NowLoadY/Robophage/resource/code/Controller/yolo/data/images/bus.jpg

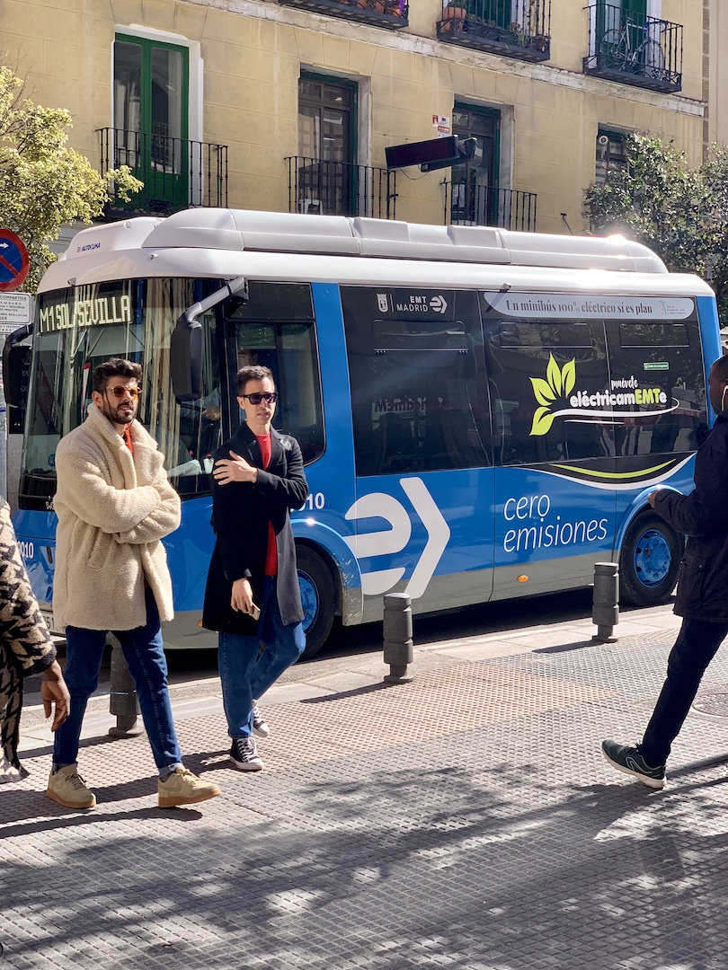
resource/code/Controller/yolo/data/images/bus.jpg
