NowLoadY/Robophage/resource/code/Controller/yolo/data/images/zidane.jpg

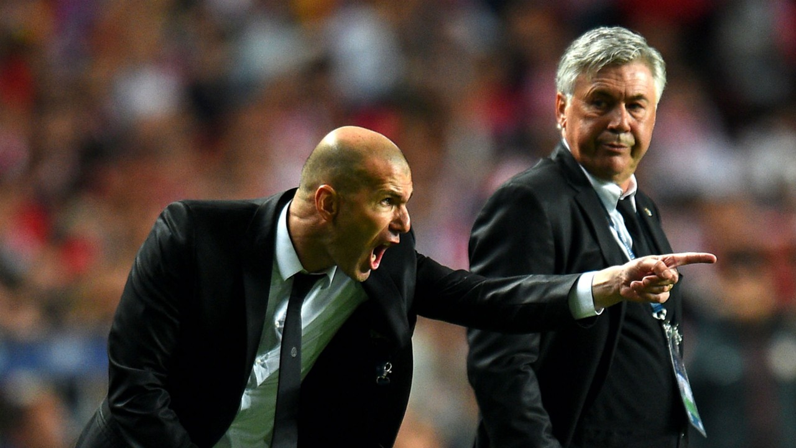
resource/code/Controller/yolo/data/images/zidane.jpg
