NowLoadY/Robophage/resource/StlFiles/foot/files/battery_lock.jpg

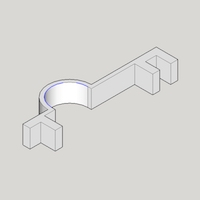
resource/StlFiles/foot/files/battery_lock.jpg
