NowLoadY/Robophage/resource/StlFiles/foot/files/body_back_wall.jpg

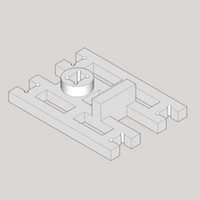
resource/StlFiles/foot/files/body_back_wall.jpg
