NowLoadY/Robophage/resource/StlFiles/foot/files/body_bottom.jpg

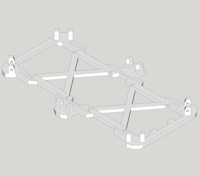
resource/StlFiles/foot/files/body_bottom.jpg
