NowLoadY/Robophage/resource/StlFiles/foot/files/body_center.jpg

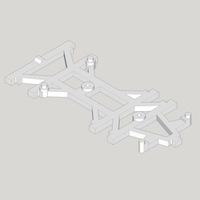
resource/StlFiles/foot/files/body_center.jpg
