NowLoadY/Robophage/resource/StlFiles/foot/files/body_side_wall.jpg

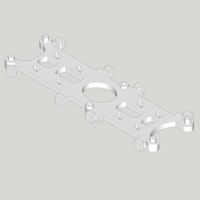
resource/StlFiles/foot/files/body_side_wall.jpg
