NowLoadY/Robophage/resource/StlFiles/foot/files/body_top.jpg

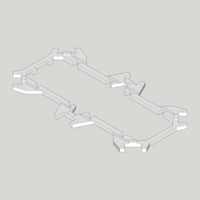
resource/StlFiles/foot/files/body_top.jpg
