NowLoadY/Robophage/resource/StlFiles/foot/files/foot_bottom.jpg

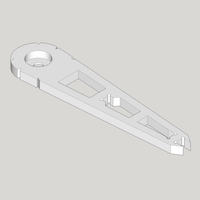
resource/StlFiles/foot/files/foot_bottom.jpg
