NowLoadY/Robophage/resource/StlFiles/foot/files/foot_ground.jpg

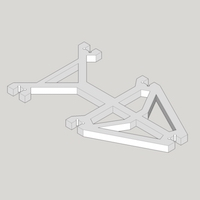
resource/StlFiles/foot/files/foot_ground.jpg
