NowLoadY/Robophage/resource/StlFiles/foot/files/foot_tip.jpg

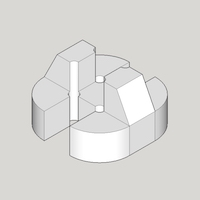
resource/StlFiles/foot/files/foot_tip.jpg
