NowLoadY/Robophage/resource/StlFiles/foot/files/foot_top.jpg

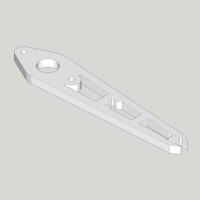
resource/StlFiles/foot/files/foot_top.jpg
