NowLoadY/Robophage/resource/StlFiles/foot/files/joint_bottom.jpg

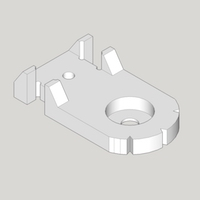
resource/StlFiles/foot/files/joint_bottom.jpg
