NowLoadY/Robophage/resource/StlFiles/foot/files/joint_cross.jpg

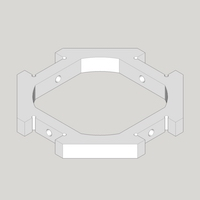
resource/StlFiles/foot/files/joint_cross.jpg
