NowLoadY/Robophage/resource/StlFiles/foot/files/joint_top.jpg

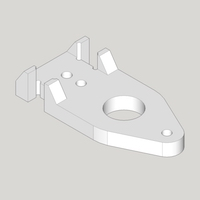
resource/StlFiles/foot/files/joint_top.jpg
