NowLoadY/Robophage/resource/StlFiles/foot/files/leg_bottom.jpg

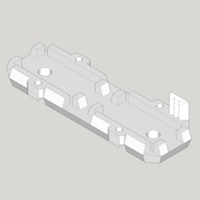
resource/StlFiles/foot/files/leg_bottom.jpg
