NowLoadY/Robophage/resource/StlFiles/foot/files/leg_top.jpg

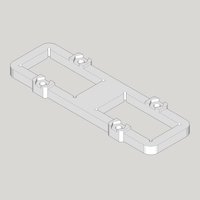
resource/StlFiles/foot/files/leg_top.jpg
