NowLoadY/Robophage/resource/StlFiles/foot/files/M2_6mm.JPG

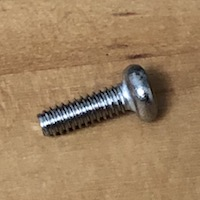
resource/StlFiles/foot/files/M2_6mm.JPG
