NowLoadY/Robophage/resource/StlFiles/foot/files/M2_10mm.JPG

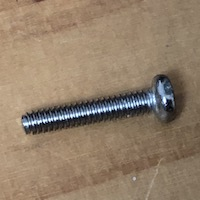
resource/StlFiles/foot/files/M2_10mm.JPG
