NowLoadY/Robophage/resource/StlFiles/foot/files/M2_30mm.JPG

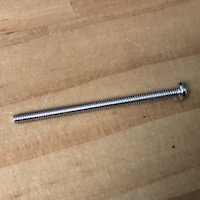
resource/StlFiles/foot/files/M2_30mm.JPG
