NowLoadY/Robophage/resource/StlFiles/foot/files/M2_nut.JPG

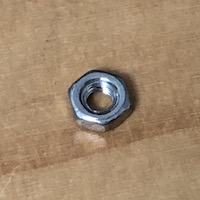
resource/StlFiles/foot/files/M2_nut.JPG
