NowLoadY/Robophage/resource/StlFiles/foot/files/mech_body.png

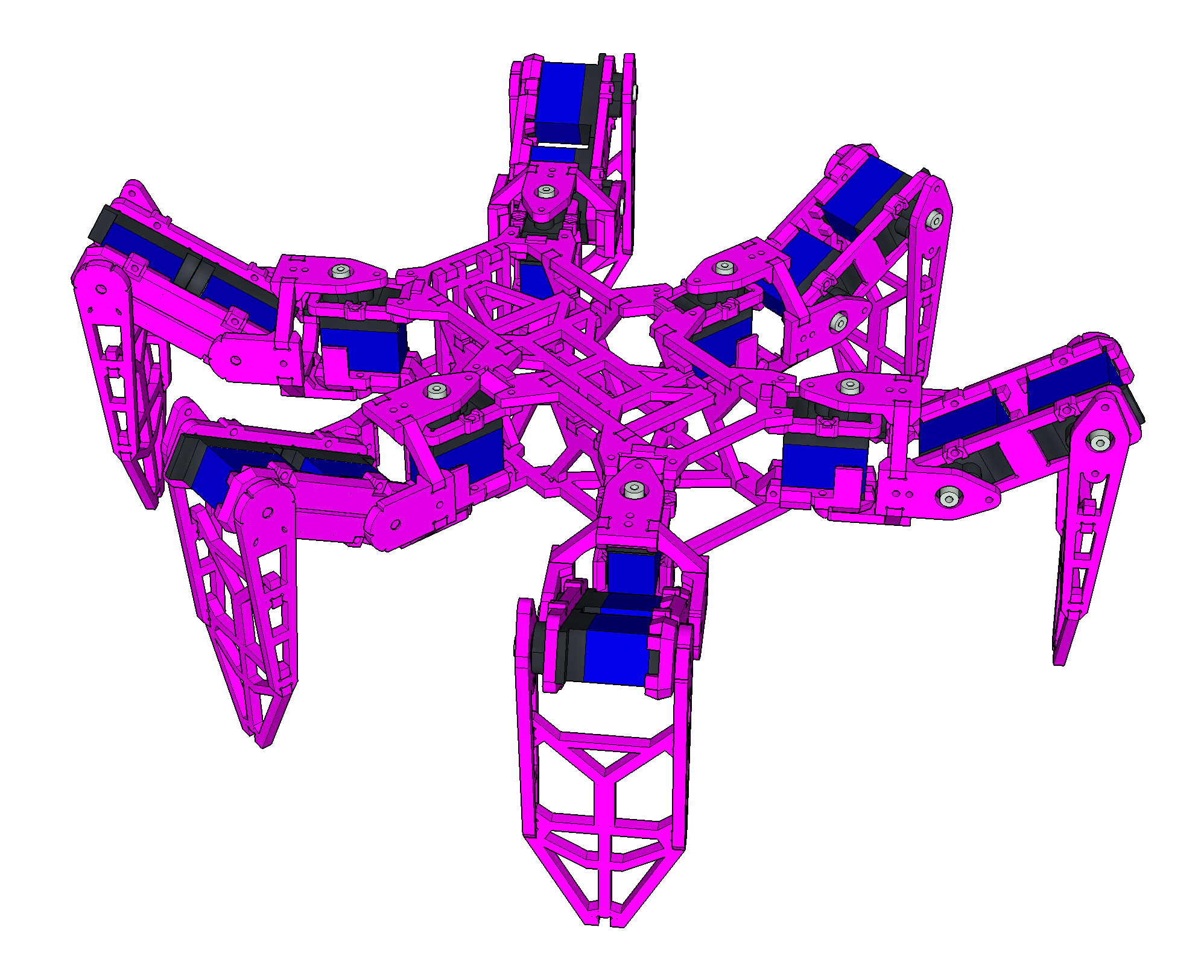
resource/StlFiles/foot/files/mech_body.png
