NowLoadY/Robophage/resource/StlFiles/foot/files/mech_leg_exploded.jpg

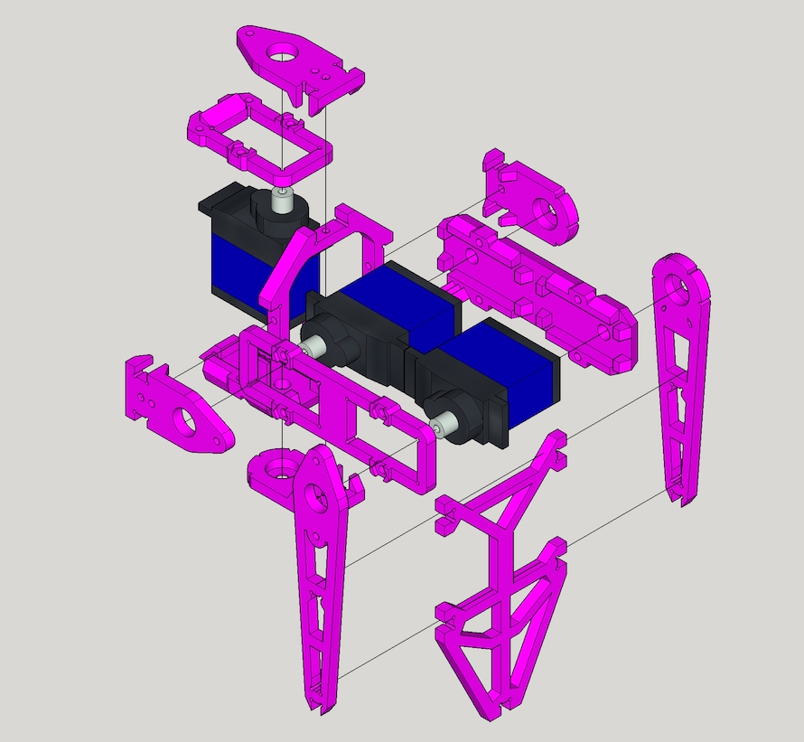
resource/StlFiles/foot/files/mech_leg_exploded.jpg
