NowLoadY/Robophage/resource/StlFiles/foot/files/pin_M4_6mm.JPG

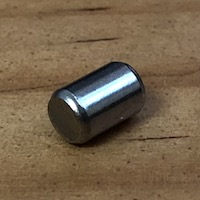
resource/StlFiles/foot/files/pin_M4_6mm.JPG
