NowLoadY/Robophage/resource/StlFiles/foot/files/thigh_bottom.jpg

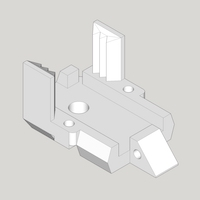
resource/StlFiles/foot/files/thigh_bottom.jpg
