NowLoadY/Robophage/resource/StlFiles/foot/files/thigh_top.jpg

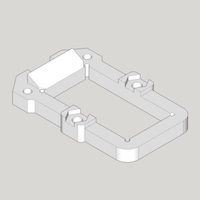
resource/StlFiles/foot/files/thigh_top.jpg
