NowLoadY/Robophage/resource/StlFiles/foot/files/tools_mount.jpg

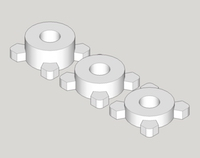
resource/StlFiles/foot/files/tools_mount.jpg
